TinyCircuits/TinyCircuits-TinyShield-microSD-ASD2201/images/ASD2201-R-Tutorial-Image-03.jpg

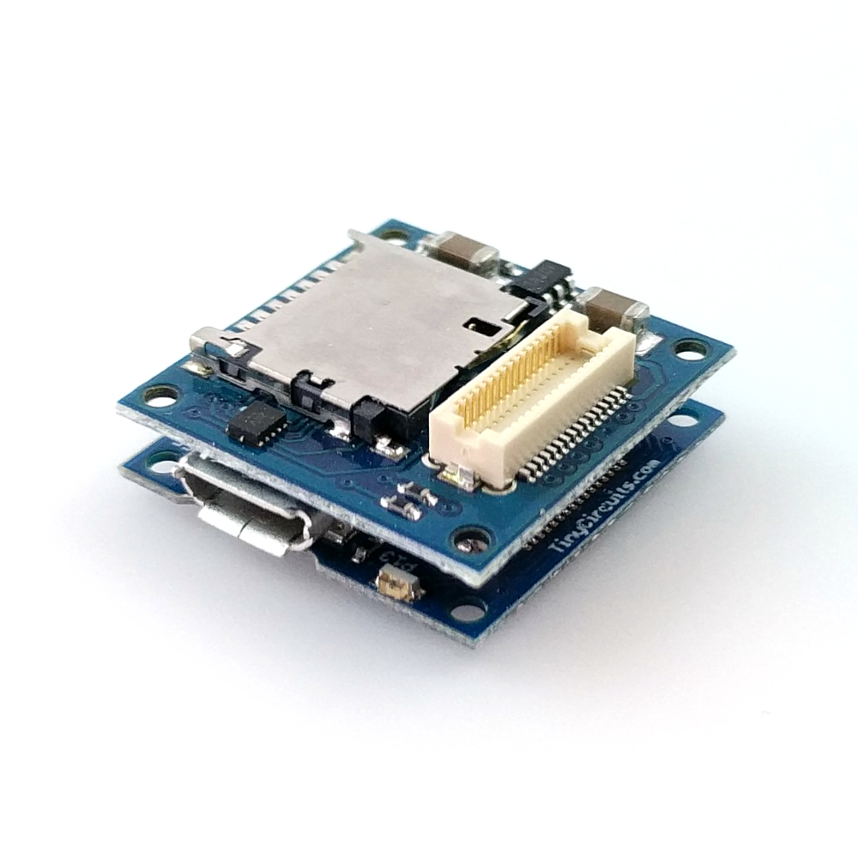
images/ASD2201-R-Tutorial-Image-03.jpg
