TinyCircuits/TinyCircuits-TinyShield-microSD-ASD2201/images/ASD2201-R-Tutorial-Image-04.png

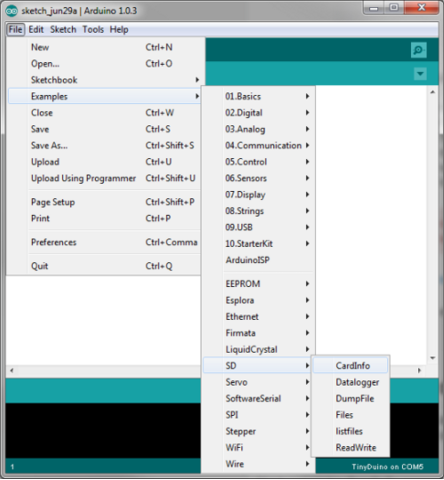
images/ASD2201-R-Tutorial-Image-04.png
